Jacquot-SFE/GvG-mixer/spice/peak-tracker/peak-detector.asc

C1: cap; 1µ
C2: cap; 1µ
D1: diode; 1N914
D2: diode; 1N914
R1: res; 100k
R2: res; 100k
R3: res; 1k
U1: UniversalOpamp2
V1: voltage; 15
V2: voltage; 15
V3: voltage; SINE(0 3 100 1 0 0 50)
Named nets: 0, V+, V-, vout
.tran 2 uic
