Jacquot-SFE/GvG-mixer/spice/baxandall/self-baxandall.asc

C1: cap; 100n
C2: cap; 100n
C3: cap; 10n
C4: cap; 10µ
C5: cap; 10n
C6: cap; 100p
R1: res; 1k8
R2: res; 1k8
R3: res; 1k
R4: res; 1k
R5: res; 12k
R6: res; {rv + 1}
R7: res; {10K001 - rv}
R8: res; 1k
R11: res; 1meg
R12: res; {10k001-rv}
R13: res; {rv+1}
U1: UniversalOpamp2
V1: voltage; 15
V2: voltage; 15
V3: voltage; SINE(0 1 100 1); AC AC 1.
Named nets: 0, V+, vout, v-
;tran 0 5 0 startup
.ac oct 12 2 100k
.step param rv 1 10K 1k
;.step param rv list 5k 5k001
